MR-DOS/LowCapacitanceProbe/Simulation/probe.asc

C1: cap; {Cin}
C2: cap; 100n
C3: cap; {Cload}
C4: cap; 100n
C5: cap; 100n
C6: cap; 6p
C7: cap; 3p
C9: cap; 1p6
C10: cap; 1p
C11: cap; 2p2
C12: cap; 2p2
L1: ind2; 4n7
L2: ind2; 10n
R1: res; 10Meg
R2: res; 75
R3: res; 5k6
R4: res; 4k7
R5: res; 50
R6: res; 42
R7: res; 56
R8: res; 1p
R9: res; 10
R10: res; 1Meg
R11: res; 47
R12: res; 5k6
R13: res; 4k7
R14: res; 50
R15: res; 100k
R16: res; 1Meg
U1: BF998
U2: BF998
V1: voltage; 5
V2: voltage; ""; AC 1
V3: voltage; ""; AC 1
V4: voltage; 4.1
V5: voltage; ""; AC 1
V6: voltage; ""; AC 1
V7: voltage; {Vg2}
Named nets: 0, Vout, Vin, Vout_orig, Vin_orig
;op 200m startup
.ac dec 801 100k 10G
.step param Cin 1.5p 3p 0.5p
.options plotwinsize=0 numdgt=15
Options for higher accuracy simulation
Set solver from Normal to Alternate! (There is no SPICE command for that, at least until LTSpice 24.1)
Simulation settings
Variable input capacitor for coarse gain tuning
These resistors increase stability of the amplifier.
Otherwise, the transistor can oscillate with
capacitive high impedance on input.
.param Cin=2.25p
This divider shall be done by
a multi-turn trimmer to allow small
corrections of gain.
The transistor shall run at <6 V to prevent
damage in case of total reflection of short
output pulse on open end of cable.
R2 has to be >50 Ohm to match the circuit
to 50 Ohm system due to output impedance
of the transistor.
Expected noise voltage on the 1M
resistor with 1 GHz bandwidth is
about 4 mV, thus about 1.2 mV
on output.
Note that this simulation does not count with realistic parasitic capacitances!
Manufacturing variance of the tranistor is not simulated!
All of the stabilising resistors as well as input capacitor need to be fine-tuned in reality.
Each device may be so different so fine-tuning may be needed for each piece.
Simulation results above 1 GHz are likely to be very unrealistic.
Original non-RF-stabilised design
>0.8 dB peaking before fall-off
2 dB flatness to approx. 1.4 GHz
6 dB flatness to approx. 1.87 GHz
First resonant notch at 3.1 GHz
Resonant peak at 3.5 GHz
Roll-off approx. 9.5 dB / octave
Improved RF design
<0.1 dB peaking before fall-off
2 dB flatness to approx. 1.68 GHz
6 dB flatness to approx. 3.3 GHz
Resonant notch at 5.9 GHz
Resonant peak at 15 GHz
Roll-of approx. 3.6 dB / octave
High quality RF capacitor C2 is required, recommended
is Kyocera/AVX 531Z104KT16T for example.
;noise V(Vout) V2 dec 801 1 4G
.step param Vg2 0 2 1
.step param Cload 1.05p 4.15p 0.5p
.param Vg2=2.5
Variableload capacitor (varicap) for fine gain tuning
Gate 2 bias, sets output impedance and roll-off behaviour
